filcarv/photodiode/Pics/IMG-5013.jpg

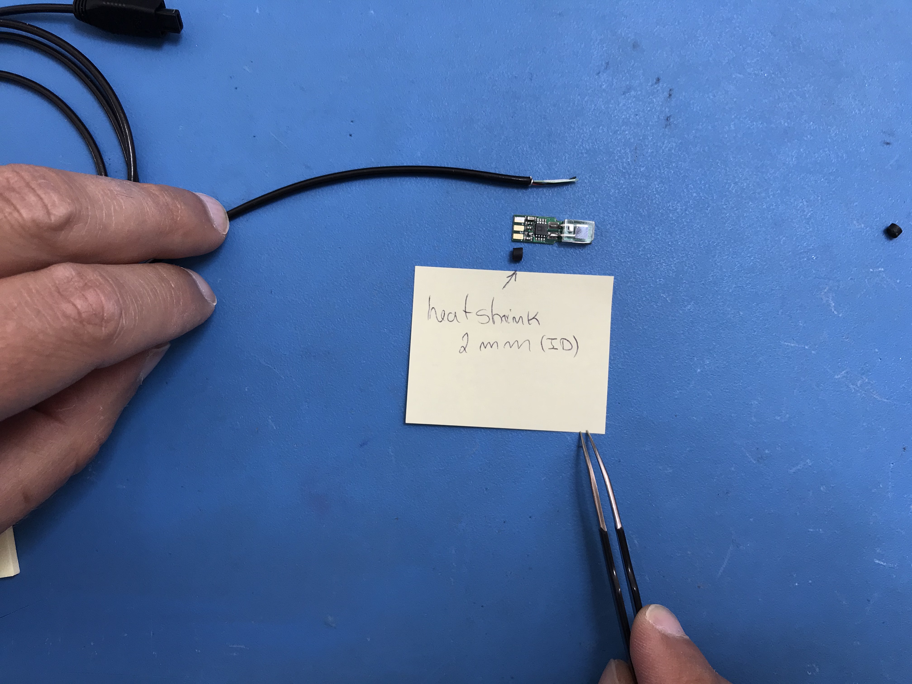
Pics/IMG-5013.jpg
