filcarv/photodiode/Pics/IMG-5025.jpg

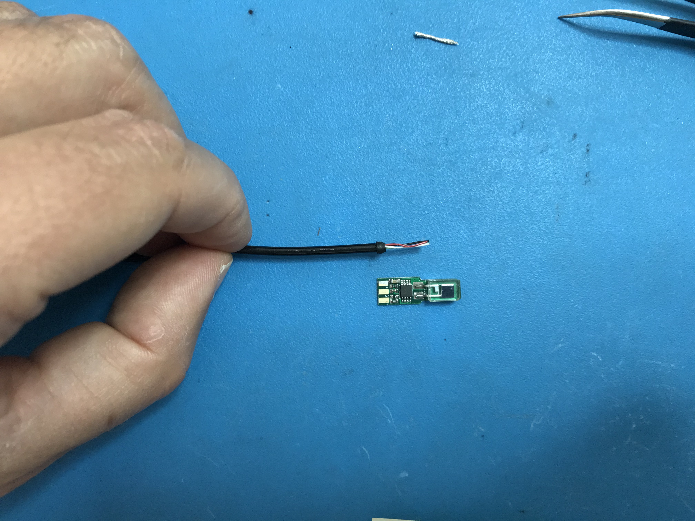
Pics/IMG-5025.jpg
